sini6a/internet-radio-speaker/Pictures/internet-radio-speaker.png

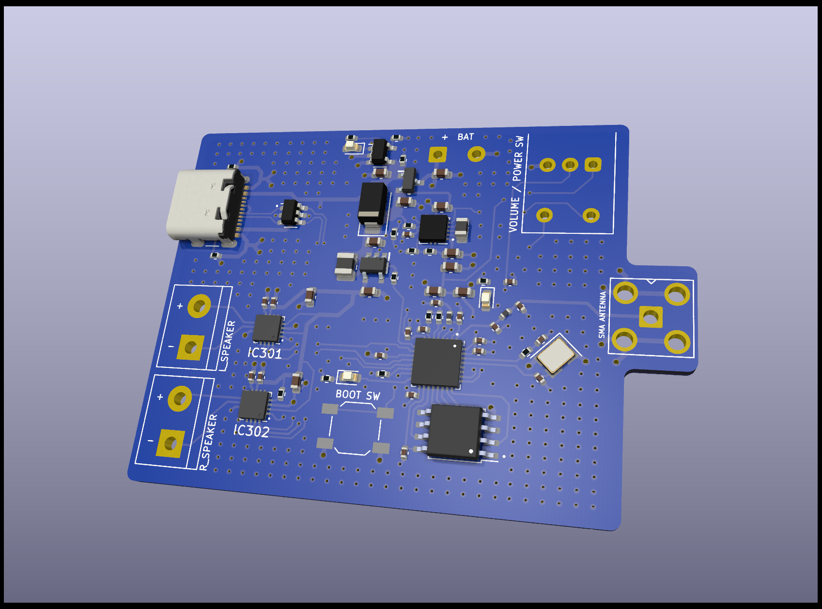
Pictures/internet-radio-speaker.png
